team-continue/Pochi/pochi_rl/pkg_4leg_assem2/meshes/RS02.stl

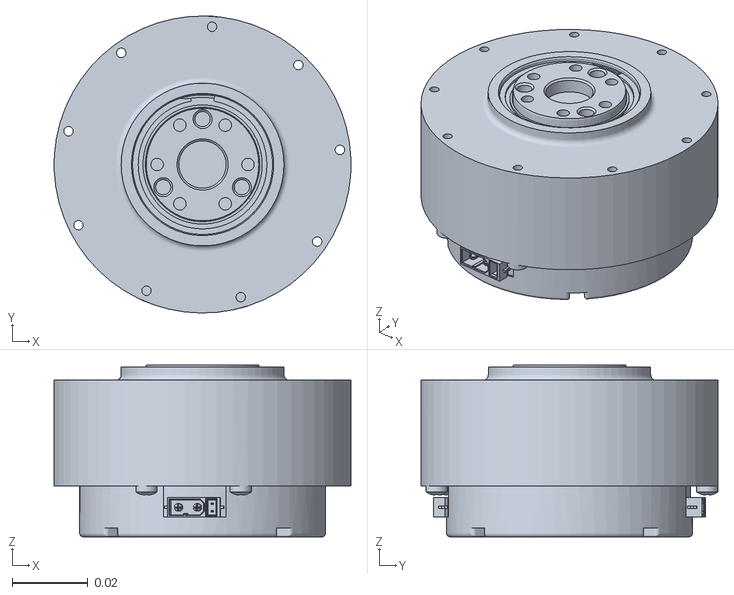
[picture p12: CAD file, 2026-09-01]
pochi_rl/pkg_4leg_assem2/meshes/RS02.stl
0.0785 x 0.0785 x 0.0454
