team-continue/Pochi/pochi_rl/assets/pochi/meshes/base_link.obj

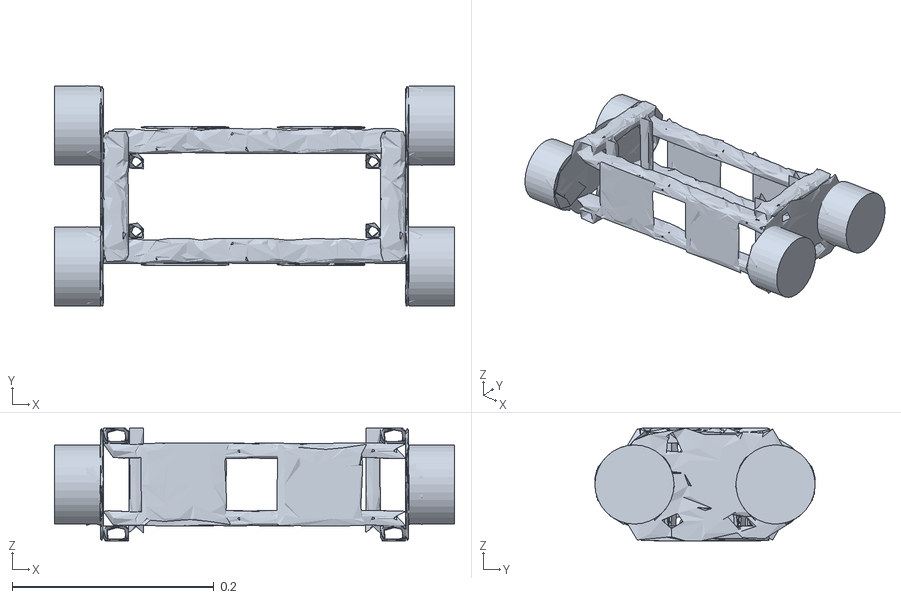
[picture p13: CAD file, 2026-09-01]
pochi_rl/assets/pochi/meshes/base_link.obj
0.397 x 0.219 x 0.112
