team-continue/Pochi/pochi_rl/assets/pochi/meshes/FL_shank.obj

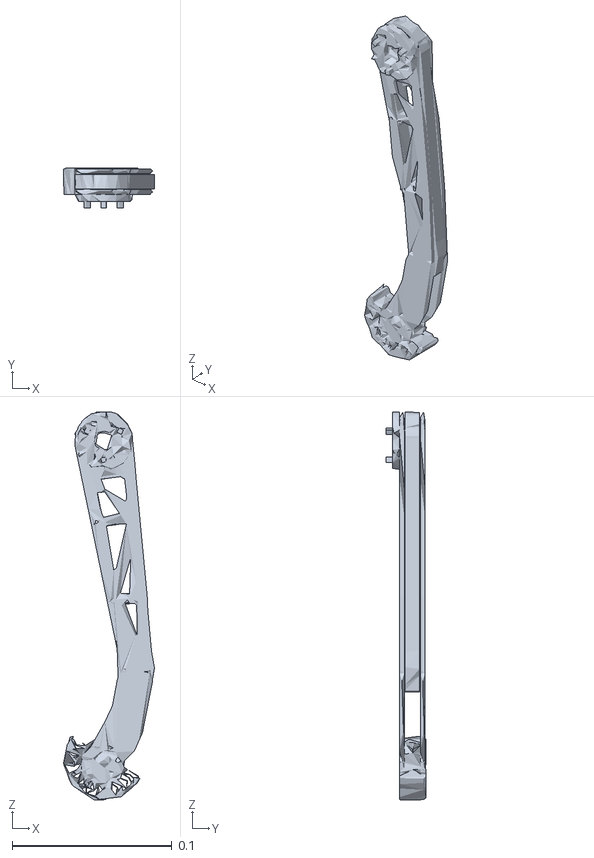
[picture p14: CAD file, 2026-09-01]
pochi_rl/assets/pochi/meshes/FL_shank.obj
0.0569 x 0.025 x 0.243
