team-continue/Pochi/pochi_rl/pkg_4leg_assem2/meshes/carbon_plate_hip_4__3mm_x4_.stl

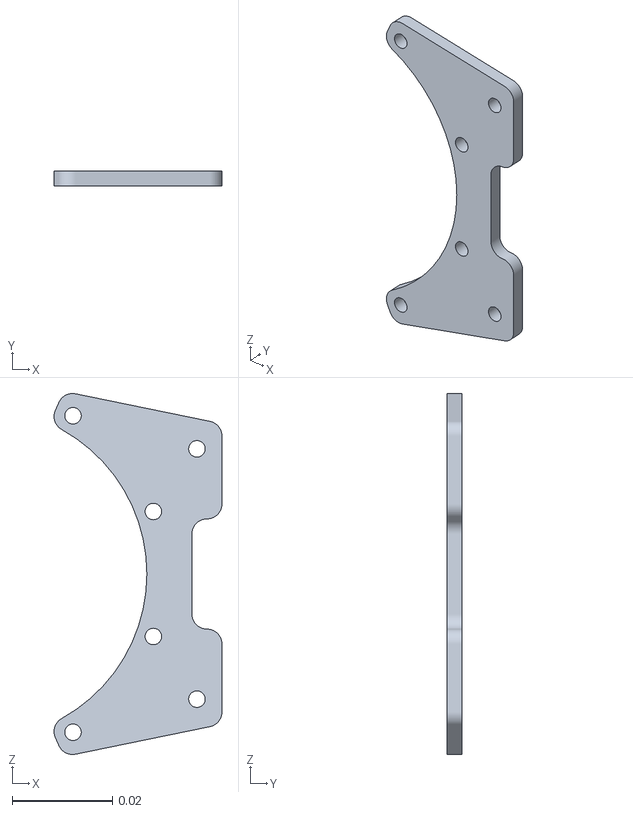
[picture p15: CAD file, 2026-09-01]
pochi_rl/pkg_4leg_assem2/meshes/carbon_plate_hip_4__3mm_x4_.stl
0.0335 x 0.003 x 0.0721
