team-continue/Pochi/pochi_rl/pkg_4leg_assem2/meshes/Body_pipe1_2_x__25_15_1_5_134_x4_.stl

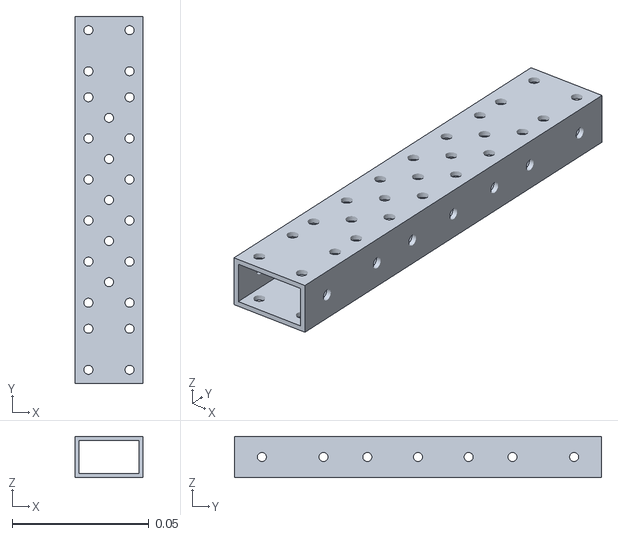
[picture p16: CAD file, 2026-09-01]
pochi_rl/pkg_4leg_assem2/meshes/Body_pipe1_2_x__25_15_1_5_134_x4_.stl
0.025 x 0.134 x 0.015
