team-continue/Pochi/pochi_rl/pkg_4leg_assem2/meshes/Part_1_3.stl

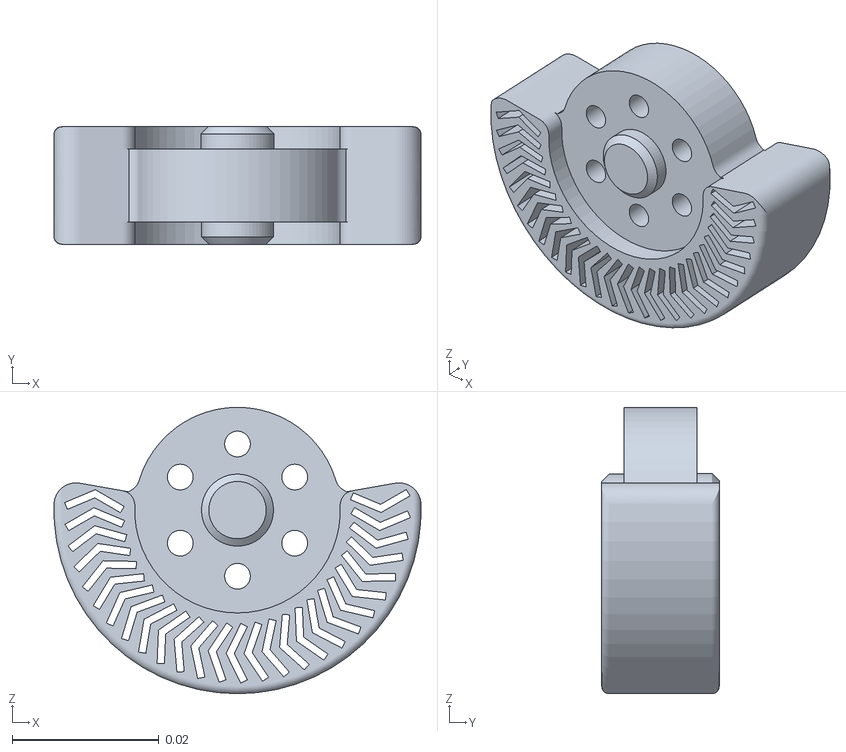
[picture p17: CAD file, 2026-09-01]
pochi_rl/pkg_4leg_assem2/meshes/Part_1_3.stl
0.05 x 0.016 x 0.039
