team-continue/Pochi/pochi_rl/pkg_4leg_assem2/meshes/Part_1_5.stl

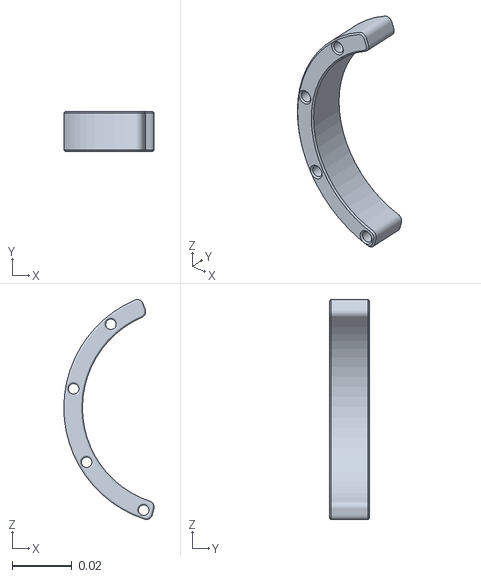
[picture p18: CAD file, 2026-09-01]
pochi_rl/pkg_4leg_assem2/meshes/Part_1_5.stl
0.0303 x 0.0135 x 0.0737
