team-continue/Pochi/pochi_rl/pkg_4leg_assem2/meshes/carbon_plate_calf_1__3mm_x8_.stl

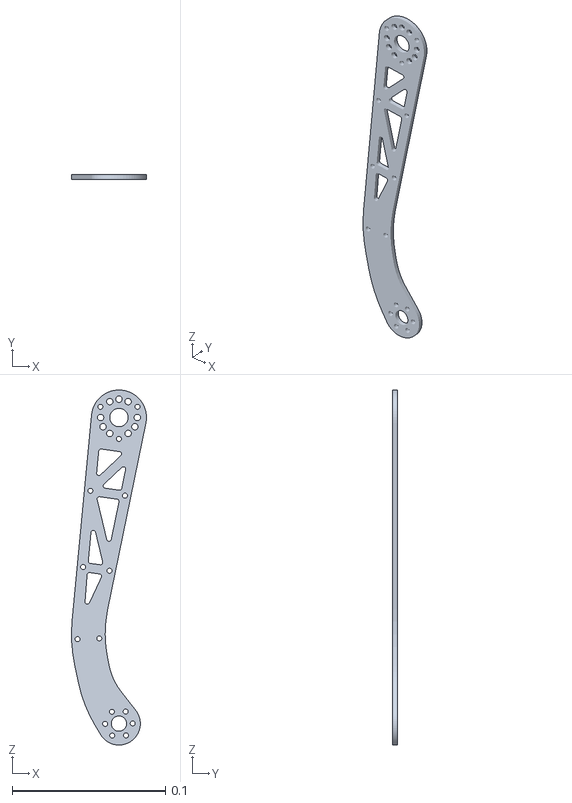
[picture p19: CAD file, 2026-09-01]
pochi_rl/pkg_4leg_assem2/meshes/carbon_plate_calf_1__3mm_x8_.stl
0.049 x 0.003 x 0.232
