team-continue/Pochi/pochi_rl/pkg_4leg_assem2/meshes/carbon_Body_plate2_y__2mm_x4_.stl

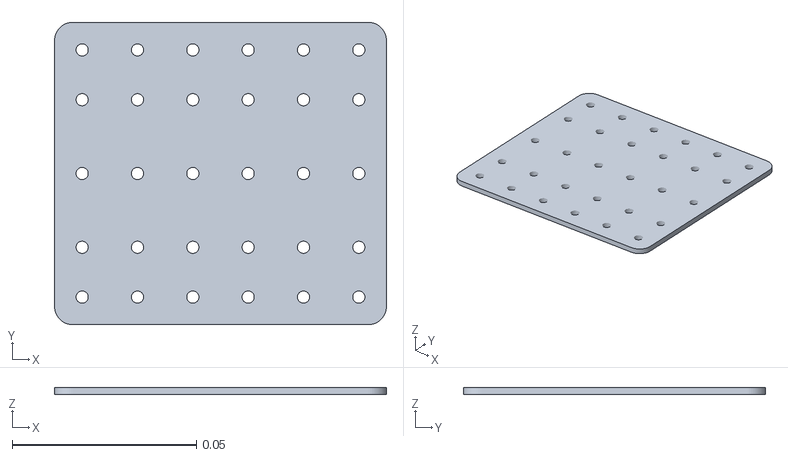
[picture p20: CAD file, 2026-09-01]
pochi_rl/pkg_4leg_assem2/meshes/carbon_Body_plate2_y__2mm_x4_.stl
0.09 x 0.082 x 0.002
