team-continue/Pochi/pochi_rl/pkg_4leg_assem2/meshes/plate_hip_3_2_spacerAl5mm__x12_.stl

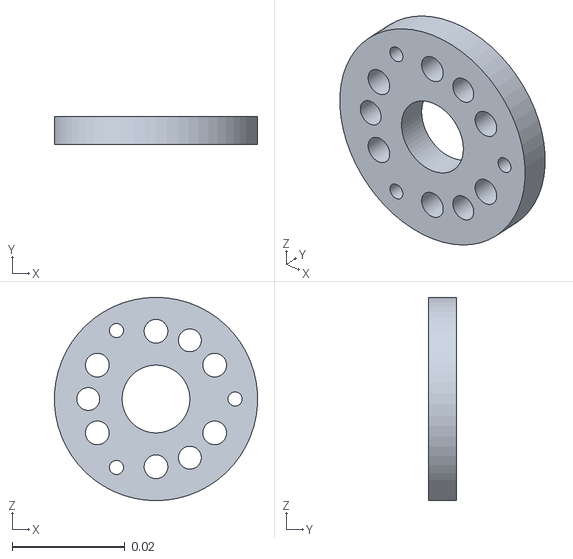
[picture p21: CAD file, 2026-09-01]
pochi_rl/pkg_4leg_assem2/meshes/plate_hip_3_2_spacerAl5mm__x12_.stl
0.0359 x 0.005 x 0.036
