team-continue/Pochi/pochi_rl/pkg_4leg_assem2/meshes/Body_pipe3_2_z__15_15_1_5_112_x4_.stl

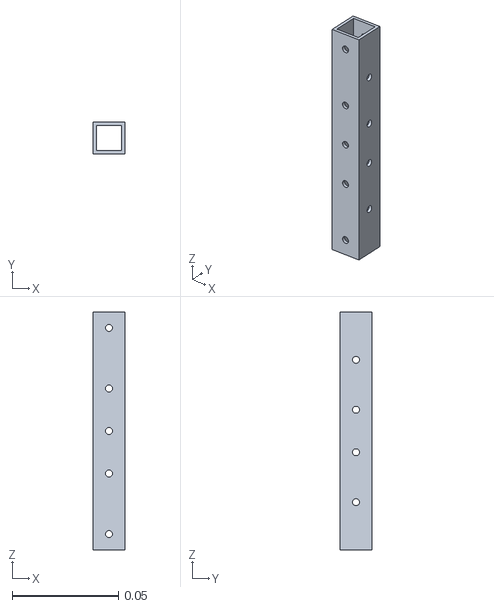
[picture p22: CAD file, 2026-09-01]
pochi_rl/pkg_4leg_assem2/meshes/Body_pipe3_2_z__15_15_1_5_112_x4_.stl
0.015 x 0.015 x 0.112
