team-continue/Pochi/pochi_rl/pkg_4leg_assem2/meshes/carbon_plate_knee1__4mm_x4_.stl

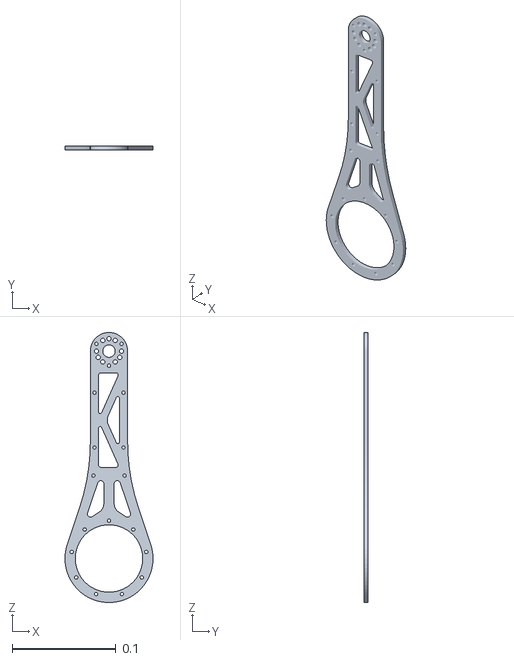
[picture p23: CAD file, 2026-09-01]
pochi_rl/pkg_4leg_assem2/meshes/carbon_plate_knee1__4mm_x4_.stl
0.085 x 0.004 x 0.26
