team-continue/Pochi/pochi_rl/pkg_4leg_assem2/meshes/Part_1_4.stl

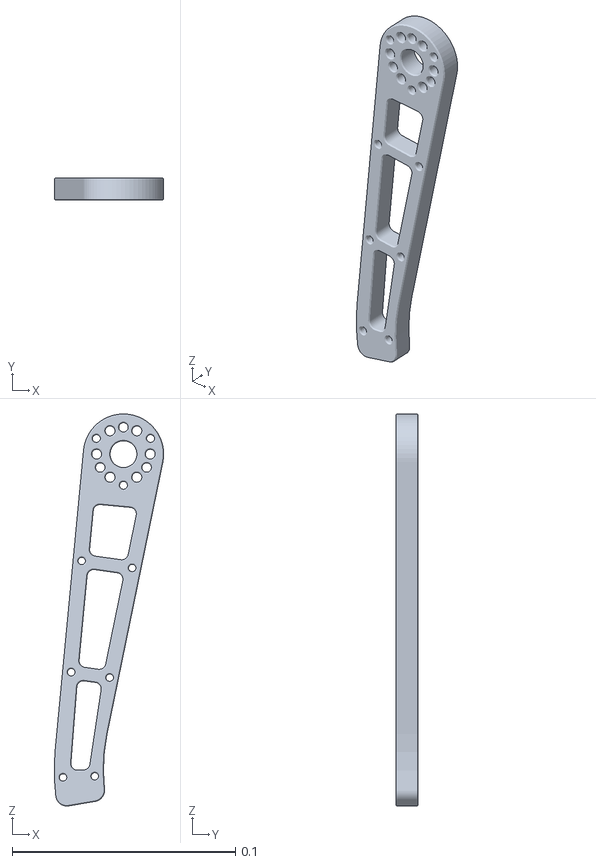
[picture p25: CAD file, 2026-09-01]
pochi_rl/pkg_4leg_assem2/meshes/Part_1_4.stl
0.049 x 0.01 x 0.176
