team-continue/Pochi/pochi_rl/pkg_4leg_assem2/urdf/pkg_4leg_assem2.urdf

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
<robot name="pkg_4leg_assem2">
    <link name="body_pipe1_2_x__25_15_1_5_134_x4_">
        <inertial>
            <mass value="0.0382239" />
            <origin xyz="-0.0075 -0.047 -0.0075" rpy="0 -0 0" />
            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
        </inertial>
        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
    </link>
    <link name="body_pipe1_2_x__25_15_1_5_134_x4__1">
        <inertial>
            <mass value="0.0382239" />
            <origin xyz="-0.0075 0.0075 0.0075" rpy="0 -0 0" />
            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
        </inertial>
        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
    </link>
    <link name="body_pipe1_2_x__25_15_1_5_134_x4__2">
        <inertial>
            <mass value="0.0382239" />
            <origin xyz="-0.0125 1.38778e-17 -2.11937e-18" rpy="0 -0 0" />
            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
        </inertial>
        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
    </link>
    <link name="body_pipe1_2_x__25_15_1_5_134_x4__3">
        <inertial>
            <mass value="0.0382239" />
            <origin xyz="-0.0125 0 -4.55864e-19" rpy="0 -0 0" />
            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
        </inertial>
        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
    </link>
    <link name="body_pipe1_2_x__25_15_1_5_134_x4___21__loop_closure">
        <inertial>
            <mass value="1e-09" />
            <origin xyz="0 0 0" rpy="0 -0 0" />
            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
        </inertial>
    </link>
    <link name="body_pipe2_y__25_15_1_5_300_x4_">
        <inertial>
            <mass value="0.0864583" />
            <origin xyz="0.0075 -0.145 -0.00675" rpy="0 -0 0" />
            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
        </inertial>
        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
    </link>
    <link name="body_pipe2_y__25_15_1_5_300_x4__1">
        <inertial>
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
        <inertial>
            <mass value="0.00199136" />
            <origin xyz="4.00266e-20 0.0165238 5.82372e-20" rpy="0 -0 0" />
            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
        </inertial>
        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
    </link>
    <link name="m3_25mm_6">
        <inertial>
            <mass value="0.00199136" />
            <origin xyz="4.00266e-20 0.0165238 5.82372e-20" rpy="0 -0 0" />
            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
        </inertial>
        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
    </link>
    <link name="m3_25mm_7">
        <inertial>
            <mass value="0.00199136" />
            <origin xyz="4.00266e-20 0.0165238 5.82372e-20" rpy="0 -0 0" />
            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
        </inertial>
        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
    </link>
    <link name="m3_25mm_8">
        <inertial>
            <mass value="0.00199136" />
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
